cristianoag/msx-picoverse/images/2024-12-30_20-07.png

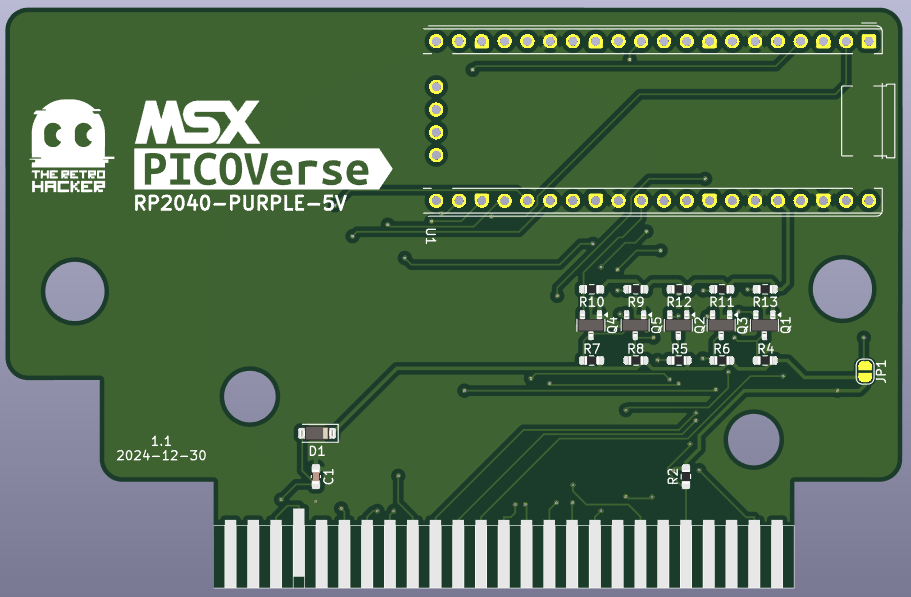
images/2024-12-30_20-07.png
