cristianoag/msx-picoverse/images/2025-01-01_09-20.png

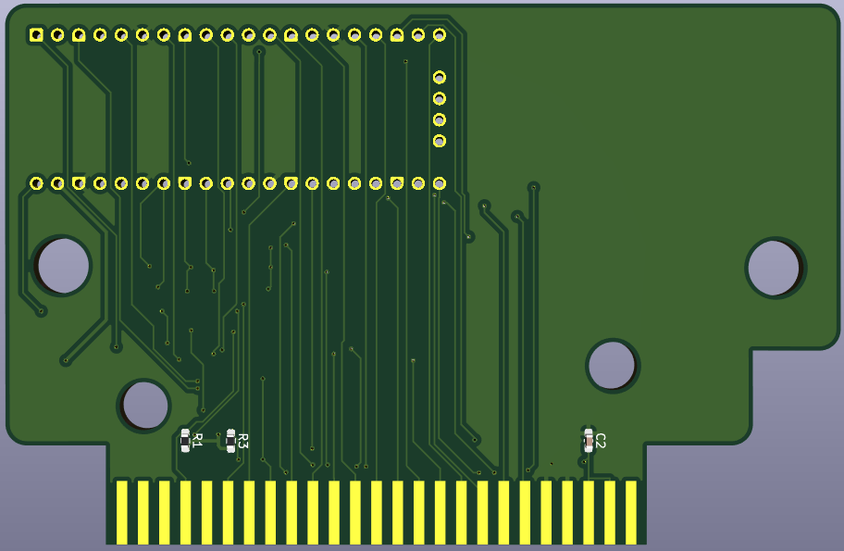
images/2025-01-01_09-20.png
