cristianoag/msx-picoverse/images/20250119_131700572_iOS.jpg

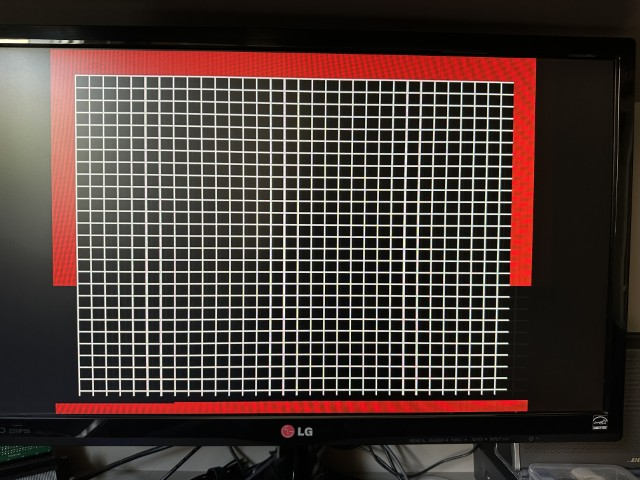
images/20250119_131700572_iOS.jpg
