cristianoag/msx-picoverse/images/Multirom3.png

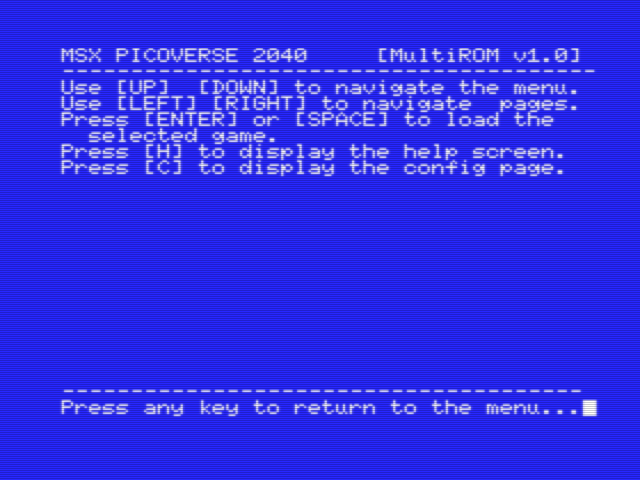
images/Multirom3.png
