cristianoag/msx-picoverse/2350/multirom/hardware/WEACT-RP2350B/1.0/msx-picoverse.kicad_sch

## KiCad design 2350/multirom/hardware/WEACT-RP2350B/1.0/msx-picoverse.kicad_sch (2025-02-15, an earlier design)

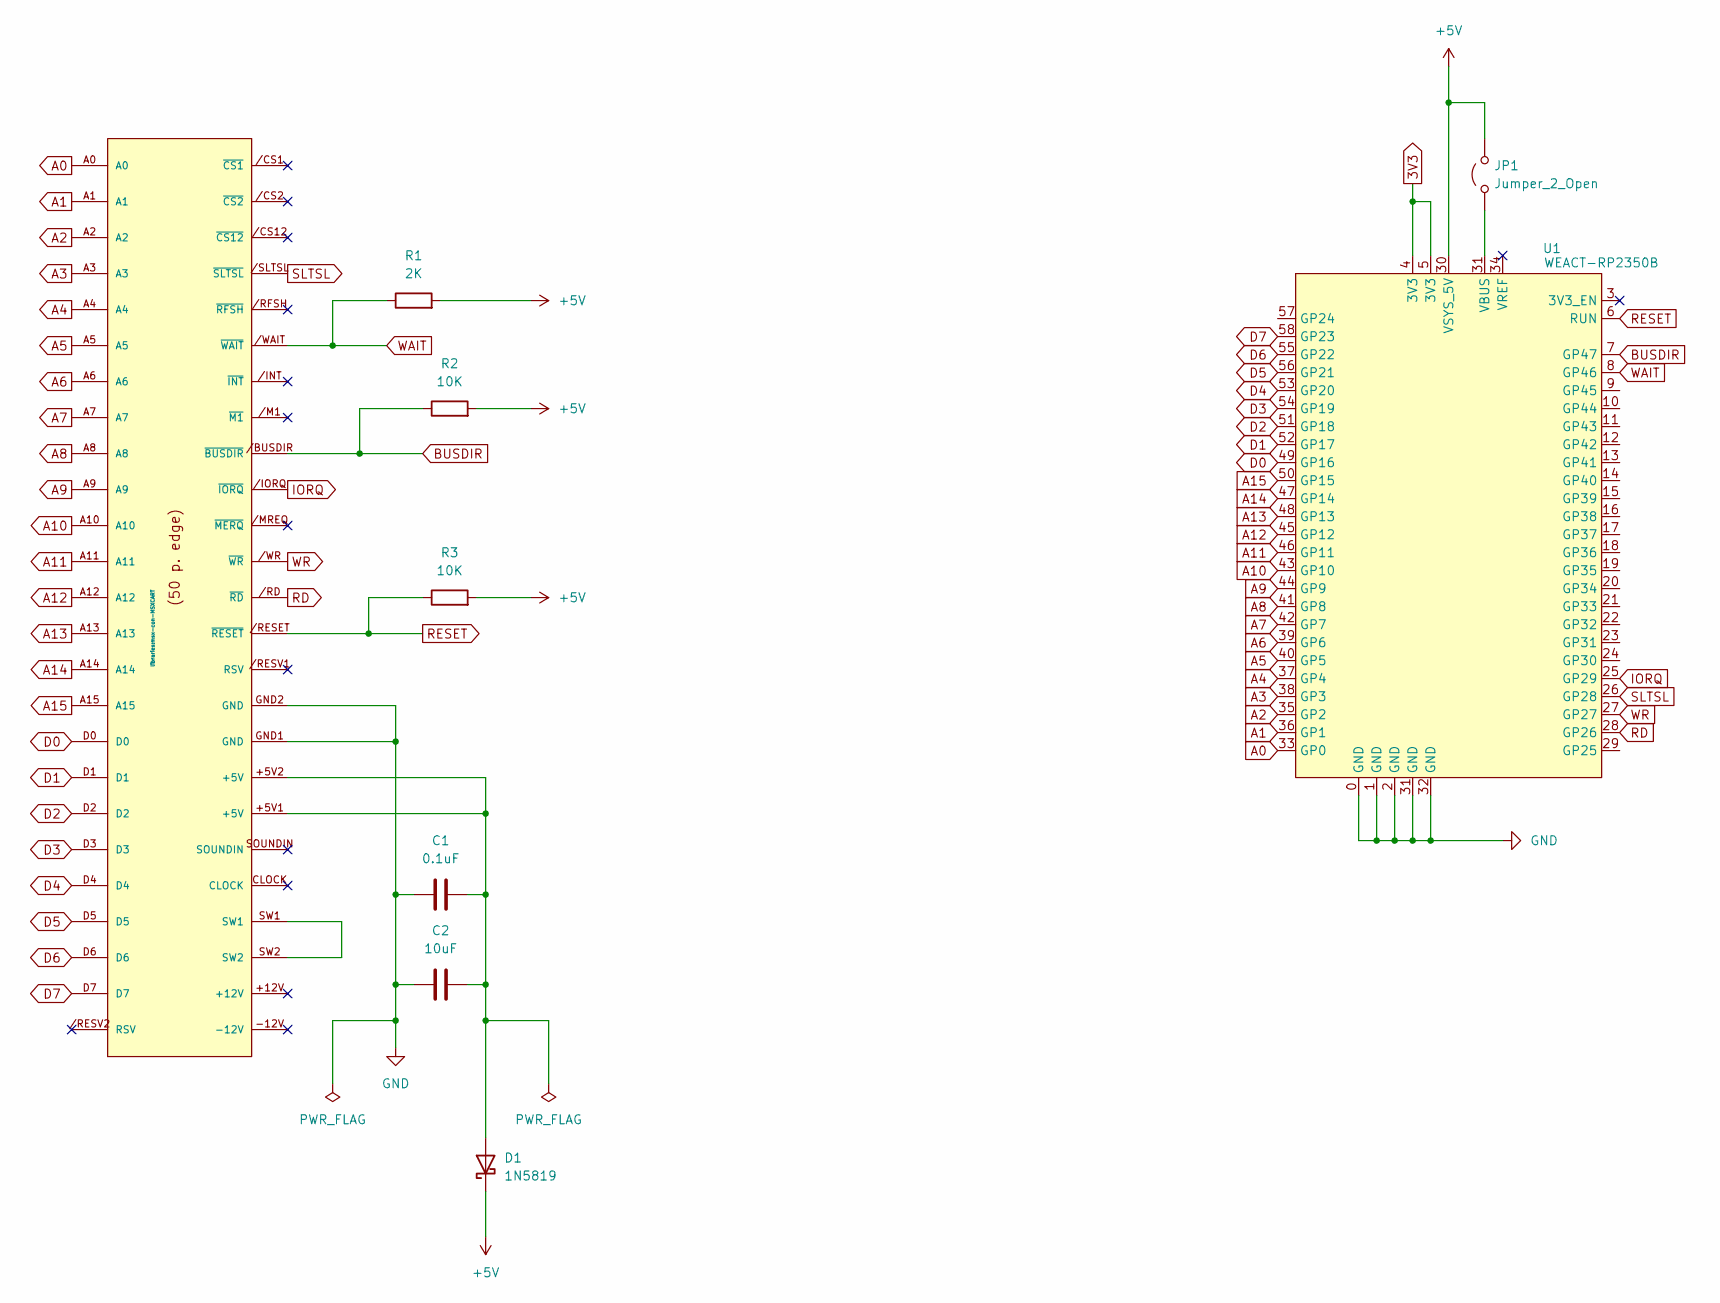
[picture p17: schematic msx-picoverse.kicad_sch]

Parts:
C1: 0.1uF; C_0603_1608Metric_Pad1.08x0.95mm_HandSolder
C2: 10uF; C_0603_1608Metric_Pad1.08x0.95mm_HandSolder
D1: 1N5819; D_SOD-123
EDG1: MSX_CON; msx-con-MSXCART
JP1: Jumper_2_Open; SolderJumper-2_P1.3mm_Open_RoundedPad1.0x1.5mm
R1: 2K; R_0603_1608Metric_Pad0.98x0.95mm_HandSolder
R2, R3: 10K; R_0603_1608Metric_Pad0.98x0.95mm_HandSolder
U1: WEACT-RP2350B

Connections:
3V3: U1.4 (3V3), U1.5 (3V3)
+5V: D1.1 (K), JP1.2 (B), R1.2, R2.2, R3.2, U1.30 (VSYS_5V)
A0: EDG1.A0, U1.33 (GP0)
A1: EDG1.A1, U1.36 (GP1)
A2: EDG1.A2, U1.35 (GP2)
A3: EDG1.A3, U1.38 (GP3)
A4: EDG1.A4, U1.37 (GP4)
A5: EDG1.A5, U1.40 (GP5)
A6: EDG1.A6, U1.39 (GP6)
A7: EDG1.A7, U1.42 (GP7)
A8: EDG1.A8, U1.41 (GP8)
A9: EDG1.A9, U1.44 (GP9)
A10: EDG1.A10, U1.43 (GP10)
A11: EDG1.A11, U1.46 (GP11)
A12: EDG1.A12, U1.45 (GP12)
A13: EDG1.A13, U1.48 (GP13)
A14: EDG1.A14, U1.47 (GP14)
A15: EDG1.A15, U1.50 (GP15)
BUSDIR: EDG1./BUSDIR (~BUSDIR), R2.1, U1.7 (GP47)
D0: EDG1.D0, U1.49 (GP16)
D1: EDG1.D1, U1.52 (GP17)
D2: EDG1.D2, U1.51 (GP18)
D3: EDG1.D3, U1.54 (GP19)
D4: EDG1.D4, U1.53 (GP20)
D5: EDG1.D5, U1.56 (GP21)
D6: EDG1.D6, U1.55 (GP22)
D7: EDG1.D7, U1.58 (GP23)
GND: C1.1, C2.1, EDG1.GND1 (GND), EDG1.GND2 (GND), U1.0 (GND), U1.1 (GND), U1.2 (GND), U1.31 (GND), U1.32 (GND)
IORQ: EDG1./IORQ (~IORQ), U1.25 (GP29)
unnamed: C1.2, C2.2, D1.2 (A), EDG1.+5V1 (+5V), EDG1.+5V2 (+5V)
unnamed: EDG1.SW1, EDG1.SW2
unnamed: JP1.1 (A), U1.31 (GND)
RD: EDG1./RD (~RD), U1.28 (GP26)
RESET: EDG1./RESET (~RESET), R3.1, U1.6 (RUN)
SLTSL: EDG1./SLTSL (~SLTSL), U1.26 (GP28)
WAIT: EDG1./WAIT (~WAIT), R1.1, U1.8 (GP46)
WR: EDG1./WR (~WR), U1.27 (GP27)
